DashSight/Pine64-Mezzanine-Card/PCB-Fabrication/v2.0-A/Photos/20200330_230518.jpg

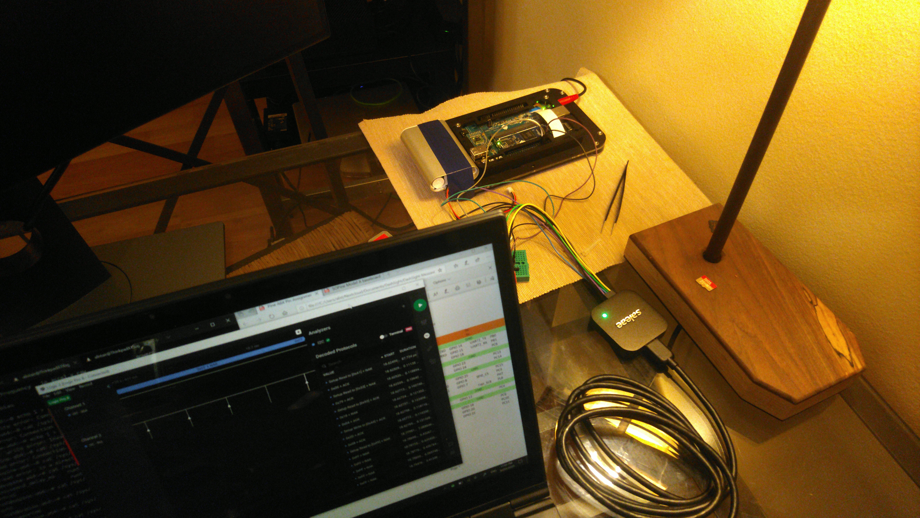
PCB-Fabrication/v2.0-A/Photos/20200330_230518.jpg
