DashSight/Pine64-Mezzanine-Card/PCB-Fabrication/v2.0-A/Photos/DashSight-Acceleromter-NotWorking.png

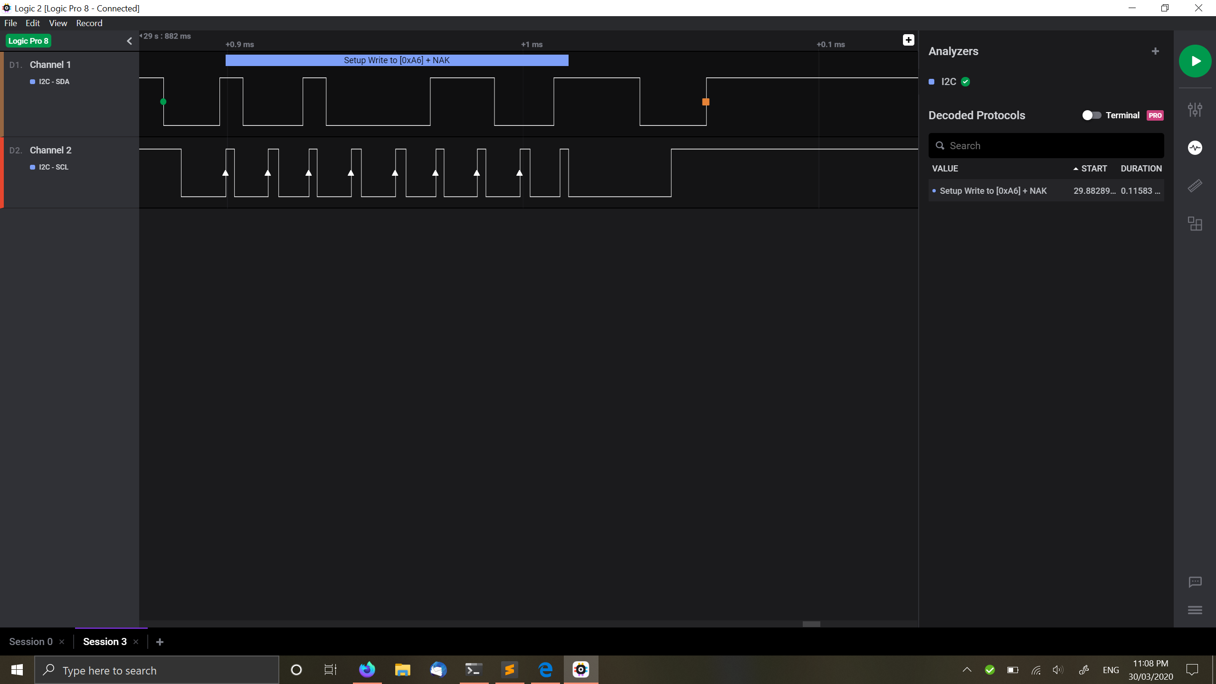
PCB-Fabrication/v2.0-A/Photos/DashSight-Acceleromter-NotWorking.png
