DashSight/Pine64-Mezzanine-Card/PCB-Fabrication/v2.0-A/Photos/DashSight-Acceleromter-Working-Analouge.png

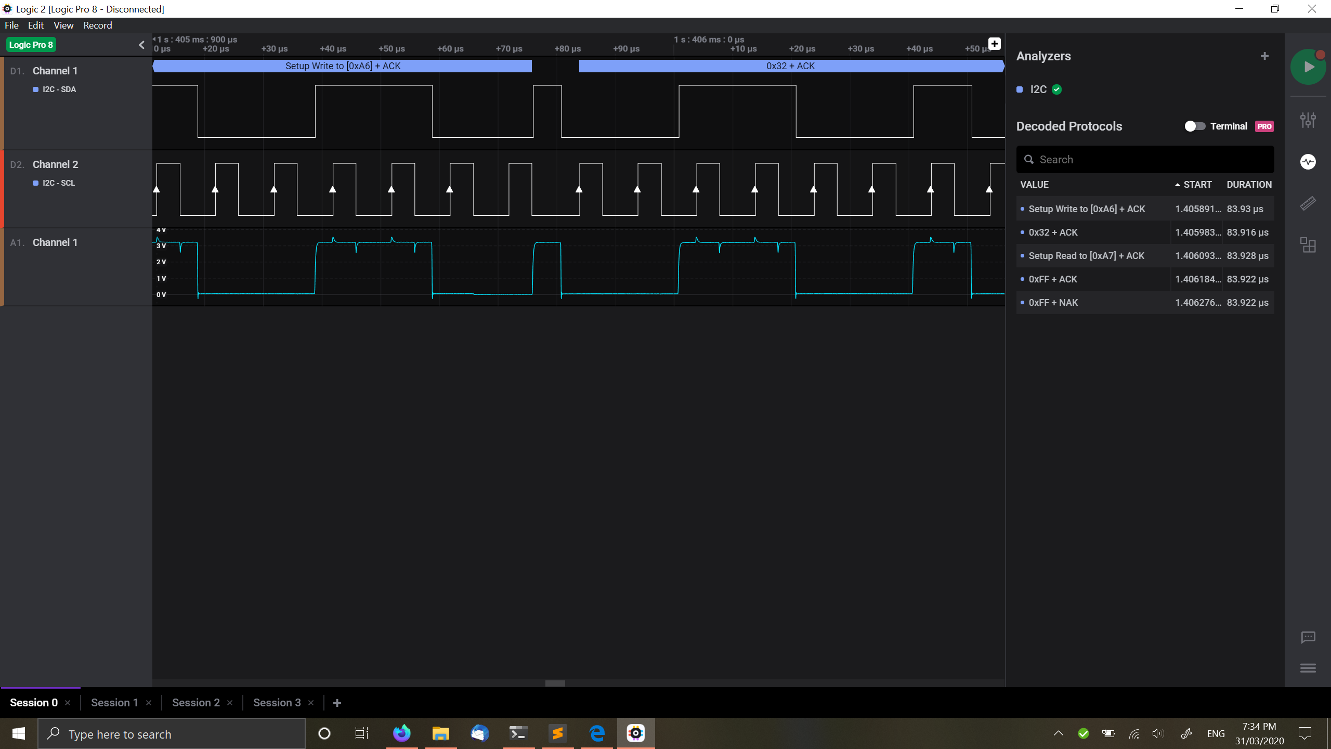
PCB-Fabrication/v2.0-A/Photos/DashSight-Acceleromter-Working-Analouge.png
