DashSight/Pine64-Mezzanine-Card/PCB-Fabrication/v2.0-A/Photos/DashSight-Acceleromter-Working.png

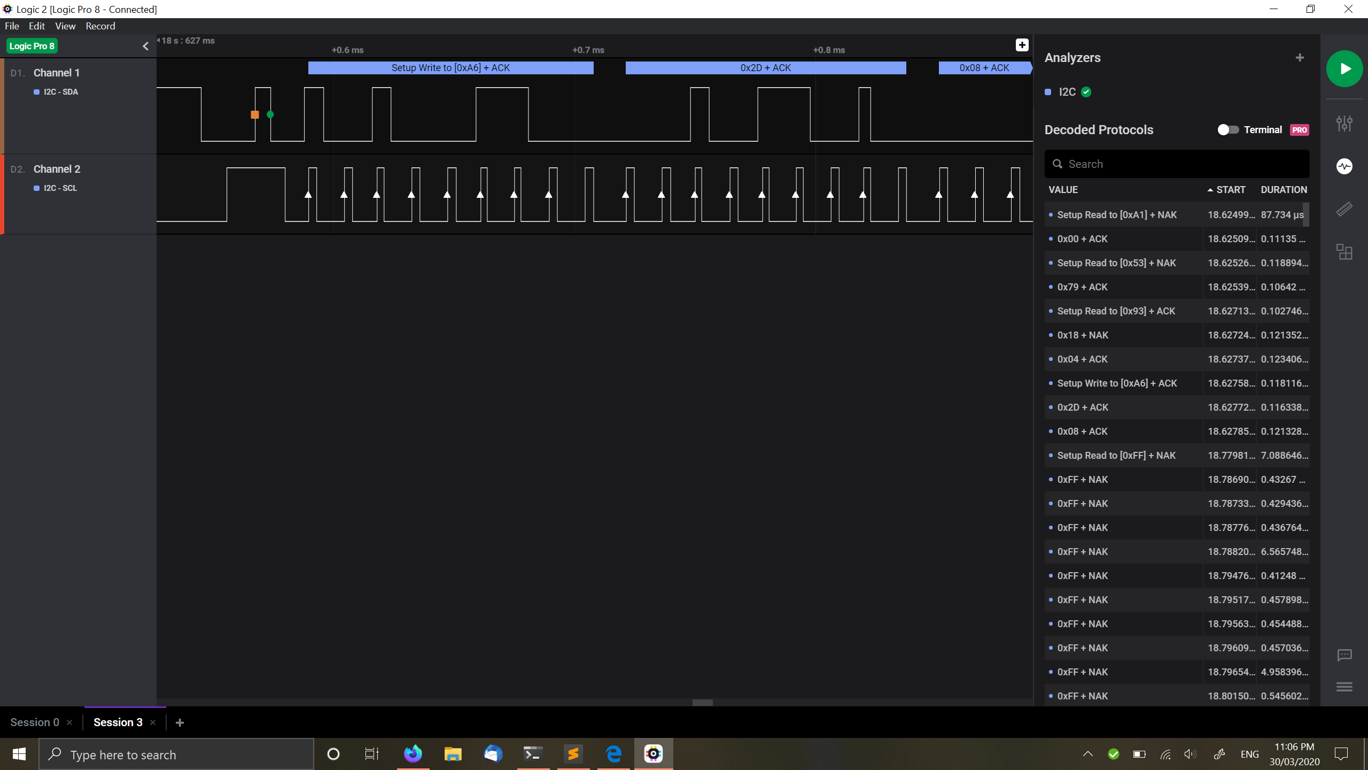
PCB-Fabrication/v2.0-A/Photos/DashSight-Acceleromter-Working.png
