DashSight/Pine64-Mezzanine-Card/PCB-Fabrication/v3.0/Photos/Photo6.jpg

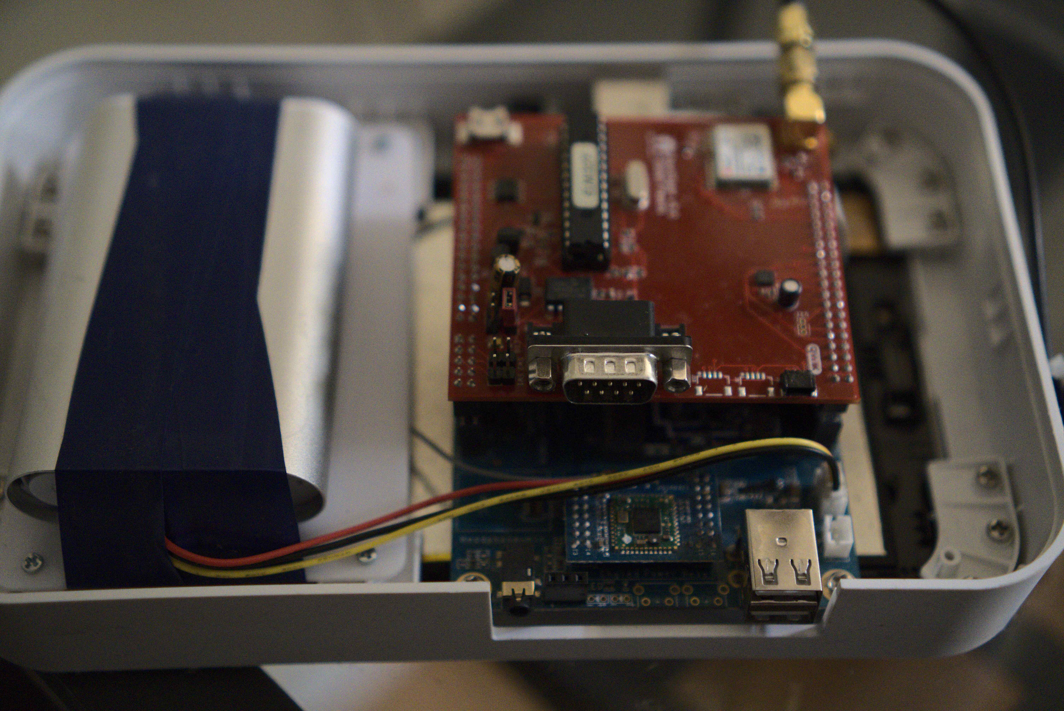
PCB-Fabrication/v3.0/Photos/Photo6.jpg
